Starefossen/snekkerbua/prosjekter/hanna/docs/generated/kappliste.md

<!-- GENERERT AV generate_loftbed.py / tools/gen_doc_tables.py.
     IKKE REDIGER FOR HÅND - kjør `mise run build`. -->

# Kappliste

Alle mål i mm. Alle kutt er 90° på to nær — se merknaden under tabellene. Posisjonen er delens plass i modellen: X langs veggen (0 = venstre vegg, 1990 = høyre vegg), Y i dybden (-48 = bakveggen), Z opp fra gulvet.

Lista står i to bolker, og skillet er en regel: **en del som kommer nærmere enn 5 mm fra en endevegg, eller som står på gulvet, får sluttmålet sitt av rommet — ikke av modellen.** Rommet er hverken i vinkel eller i vater. Resten kappes ferdig på bukken.

Mål rommet før du kapper romdelene: se [byggesteg](byggesteg.md#før-steg-0--mål-rommet).

## Kapp nå — verksteddeler

| Del | Dim. | Lengde | Ant. | X | Y | Z |
|---|---|---:|---:|---|---|---|
| Løs plate | 18 mm plate, 574 bred | **798** | 1 | 708..1282 | -48..750 | 297..315 |
| Benkespile | 23×98 | **800** | 10 | 98..1892 (fordelt) | -48..752 | 297..320 |
| Køyespile | 23×98 | **800** | 14 | 20..1970 (fordelt) | -48..752 | 1500..1523 |
| Rekkverksavstiver | 23×98 | **180** | 8 | 157,4..1832,6 (fordelt) | 752..775 | 1721..1901 |
| Benkespileledd | 36×48 | **547** | 2 | 98..1892 (fordelt) | 704..740 | 249..297 |
| Stigekloss | 36×48 | **36** | 8 | 835..1155 (fordelt) | 752..788 | 201..1194 (fordelt) |
| Endebjelke | 36×98 | **836** | 2 | 98..1892 (fordelt) | -48..788 | 1304..1402 |
| Fotbrettgavl (løs del) | 36×98 | **272** | 2 | 787..1203 (fordelt) | 216..488 | 0..98 |
| Benkevange, bak (gjennomgående) | 48×68 | **1794** | 1 | 98..1892 | -48..0 | 229..297 |
| Bordbærelekt, bak | 48×68 | **1794** | 1 | 98..1892 | -48..0 | 614..682 |
| Avstivningslekt under plate | 48×68 | **750** | 2 | 785..1205 (fordelt) | 0..750 | 229..297 |
| Benkevange, front (bit) | 48×68 | **547** | 2 | 98..1892 (fordelt) | 740..788 | 229..297 |
| Fotbrettbord | 48×68 | **416** | 4 | 787..1203 | 216..488 (fordelt) | 98..146 |
| Rungetrinn | 48×68 | **320** | 4 | 835..1155 | 720..788 | 249..1242 (fordelt) |
| Kilelekt under platens forkant (skråkappet) | 48×68 | **77** | 2 | 708..1282 (fordelt) | 702..750 | 229..297 |

**63 deler.** Rommet bestemmer ingen mål på disse. Kapp dem ferdig med én gang.

## Kapp når rommet er ferdig — romdeler

| Del | Dim. | Lengde | Ant. | Kapp på stedet | X | Y | Z |
|---|---|---:|---:|---|---|---|---|
| Endespile | 23×98 | **764** | 2 | nominell — bredden strekes opp | 0..1990 (fordelt) | -12..752 | 297..320 |
| Stigevange | 36×48 | **1871** | 2 | **+20** — trimmes i bunn | 787..1203 (fordelt) | 752..788 | 0..1871 |
| Endelist | 36×48 | **98** | 2 | **+10** i veggenden — finkappes | 0..1990 (fordelt) | -12..24 | 249..297 |
| Endelist, fremre | 36×48 | **98** | 2 | **+10** i veggenden — finkappes | 0..1990 (fordelt) | 716..752 | 249..297 |
| Hjørnestolpe, front | 36×98 | **2037** | 2 | **+20** — trimmes i bunn · siden mot veggen strekes opp ved bul | 0..1990 (fordelt) | 752..788 | 0..2037 |
| Hjørnestolpe, bak (veggside) | 36×98 | **1402** | 2 | **+20** — trimmes i bunn · siden mot veggen strekes opp ved bul | 0..1990 (fordelt) | -48..-12 | 0..1402 |
| Rekkverksbord, front | 36×98 | **832** | 4 | **+10** i veggenden — finkappes | 3..1987 (fordelt) | 716..752 | 1653..1969 (fordelt) |
| Stubbefot | 48×68 | **229** | 4 | **+20** — trimmes i bunn | 577..1413 (fordelt) | -48..788 (fordelt) | 0..229 |
| Sidevange, øvre | 48×98 | **1984** | 2 | **+10** i hver ende — finkappes | 3..1987 | -48..752 (fordelt) | 1402..1500 |

**22 deler.** Kapp dem med overmålet i kolonnen «Kapp på stedet», og finkapp på stedet:

* **Står på gulvet:** kapp 20 mm for lang. Gulvet legges først. Så trimmes foten til rammen står i vater. Strek opp med avstandskloss — meddrag.
* **Står på gulvet inntil endevegg — hjørnestolpene:** samme trimming i bunn, og i tillegg strekes siden. Stolpen står helt inntil veggen uten klaring, så en bul i veggen må tas i treet: hold stolpen i lodd på plass, strek opp veggsiden med avstandskloss og høvle av til den står i lodd inntil veggen. Ikke legg på noe i bredden — den nominelle dimensjonen står, det er bare bulen som går av.
* **Går fra vegg til vegg:** kapp 10 mm for lang i hver ende som møter vegg. Finkapp etter målt nisjebredde.
* **Bredden mot veggen:** kappes på nominell lengde. Det er BREDDEN som tilpasses, ikke lengden — ytterkanten strekes opp etter veggen så fugen blir jevn.

Kapp kanter som møter vegg eller gulv med lite bakfall. Da er det bare den synlige kanten som bestemmer fugen.

**85 deler i alt.**

«(fordelt)» betyr at delene i den raden står på flere posisjoner langs den aksen; kolonnen viser da hele området de dekker. Nøyaktige posisjoner står i [nøkkelmål](nokkelmal.md).

**Ett unntak fra «alle kutt er 90°»:** de to kilelektene under platens forkant. De sages i ett rett snitt fra full 68 mm ved roten — enden som støter mot styrelekta — ned til 27 mm ved tuppen på platens ytterkant, altså 28,0° på langs. Overkanten, den som limes mot plata, blir stående urørt i hele lengden. Håndsag eller båndsag; se steg 0 og J13b.

## Hjelpedeler — kappes, men bygges ikke inn

| Del | Dim. | Lengde | Ant. | Kapp | Brukes til |
|---|---|---:|---:|---|---|
| Vinkelkloss 25° (J8-B) — borjigg for skråskruen | 48×68 | **200** | 2 | 2 stk. skrus FLATE MOT FLATE til én kloss. ⌀18 bores VINKELRETT gjennom begge mens klossen ennå er firkantet — det er hele trikset. Først DERETTER kappes sålen av under hullet: kappsag med bladet vippet 25°, som gir en såle som står 65° på den borede flaten og dermed 25° på hullaksen. Kontrollmål: hullets munning i sålen er en ellipse på 42,6 × 18 mm — er den for kort, ble vippen satt på komplementvinkelen | klemmes mot flaten med TO tvinger, hullet over merket. ⌀18 forstnerbor og deretter forboret går NED I hullet, så boret ikke kan vandre. Dybdemerke: hold boret i jiggen til randen flukter med sålen ved hullaksen, merk av på skaftet og flytt merket 20 mm opp — det er setedybden. Brukes i J8-B |
| Vinkelkloss 30° (J10) — borjigg for skråskruen | 48×68 | **200** | 2 | 2 stk. skrus FLATE MOT FLATE til én kloss. ⌀18 bores VINKELRETT gjennom begge mens klossen ennå er firkantet — det er hele trikset. Først DERETTER kappes sålen av under hullet: kappsag med bladet vippet 30°, som gir en såle som står 60° på den borede flaten og dermed 30° på hullaksen. Kontrollmål: hullets munning i sålen er en ellipse på 36 × 18 mm — er den for kort, ble vippen satt på komplementvinkelen | klemmes mot flaten med TO tvinger, hullet over merket. ⌀18 forstnerbor og deretter forboret går NED I hullet, så boret ikke kan vandre. Dybdemerke: hold boret i jiggen til randen flukter med sålen ved hullaksen, merk av på skaftet og flytt merket 18 mm opp — det er setedybden. Brukes i J10 |

Disse er ikke med i de 85 delene over — de er ikke deler i senga, de er verktøy du sager i steg 0. Virket til dem er likevel med i [innkjøpslista](innkjopsliste.md): de står i kappeplanen for sin egen dimensjon, som alt annet du må sage.

Fordelt på dimensjon: **23×98** 34 stk. · **48×68** 20 stk. · **36×48** 16 stk. · **36×98** 12 stk. · **48×98** 2 stk. · **18 mm plate, 574 bred** 1 stk.

Sagstopp for hovedbordet 36×98: **2 stk. à 2037** · **2 stk. à 1402** · **2 stk. à 836** · **4 stk. à 832** · **2 stk. à 272** — 5 innstillinger på sagen, ikke én per del.
