Starefossen/snekkerbua/prosjekter/hanna/docs/generated/nokkelmal.md

<!-- GENERERT AV generate_loftbed.py / tools/gen_doc_tables.py.
     IKKE REDIGER FOR HÅND - kjør `mise run build`. -->

# Nøkkelmål

Alle mål i mm. X går langs rommet mellom de to veggene, Y i dybden med bakveggen på -48, Z opp fra gulvet.

## Ytre mål

| | Mål |
|---|---:|
| Bredde, vegg til vegg | 1990 |
| Dybde over alt | 836 |
| Høyde foran (stolpetopp) | 2037 |
| Høyde ved veggen (bakre stolpe) | 1402 |
| **Takhøyde i rommet senga er regnet for** | **2450** |
| Klaring over høyeste del | 413 |
| **Fri høyde under senga (gulv til spilenes underside)** | **1500** |
| Fri høyde over øvre madrass | 807 |
| Gjennomgående deler kappes til | 1984 (X 3..1987) |
| Klaring til hver vegg for disse | 3 |

En 1990 mm lang del lar seg ikke svinge inn i en 1990 mm åpning. Derfor er hver gjennomgående del 1984 mm.

## Høyder (Z)

| Z | Hva |
|---:|---|
| **0** | gulv |
| **229** | benkevangens underkant / stubbefotens topp |
| **297** | benkevangens overkant = trinn 1 = platens underside i sengestilling |
| **315** | platens overside i sengestilling |
| **320** | benkeoverflate (sittehøyde uten pute) |
| **420** | **puteoverflate — nedre soveflate og sittehøyde med pute** (V13) |
| **614** | bordbærelektas underkant |
| **634** | støttetrinnets underkant |
| **682** | trinn 2 = bordbærelektas og STØTTETRINNETS overkant = platens underside i bordstilling (X16: et trinn igjen; X9 hadde to bordklosser her) |
| **700** | **bordplate — pulthøyde** (X9) |
| **752** | ryggputens topp i sofastilling (V13) |
| **962** | trinn 3 |
| **1242** | trinn 4 |
| **1304** | endebjelkens underkant |
| **1402** | **bakre stolpetopp** = endebjelkens overkant = sidevangens underkant (fri høyde under sengen) |
| **1500** | sidevangens overkant |
| **1523** | spilebunn / madrassens underside |
| **1643** | madrassens overside (ved 120 mm madrass; lovlig band 105–130) |
| **1653** | rekkverk, nedre bånd underkant |
| **1751** | rekkverk, nedre bånd overkant |
| **1871** | rekkverk, øvre bånd underkant |
| **1969** | rekkverk, øvre bånd overkant |
| **2037** | fremre stolpetopp |

Stigningen fra gulv til spilebunn: 297 + 385 + 280 + 280 + 281 mm. Første stigning er benkevangens høyde — det er en avsats du trår opp på, ikke et klatretrinn. De 4 klatretrinnene er 280–385 mm.

## Dybdeplan (Y)

| Y | Hva |
|---:|---|
| **-48** | BAKVEGGEN — monteringsflaten. Bakre stolper, endebjelkeender og bakre stubbeføtter ligger i dette planet. Ingenting får stikke bak det.; bakre sidevange, benkevange, bordbærelekt og spilebunn — bakkant; bakre stolpes forside |
| **0** | bakre sidevanges, benkevanges og bordbærelektas forside; avstivningslektenes bakkant |
| **704** | fremre sidevange og benkevange — bakkant |
| **716** | rekkverksbordenes bakkant |
| **720** | trinnenes bakkant (hylla platen hviler på) |
| **750** | platens forkant; avstivningslektenes og kilelektenes forkant |
| **752** | fremre sidevanges forside = fremre stolpers og stigevangers bakside = spilebunnens forkant; rekkverksbordenes forkant |
| **788** | fremre stolpers og stigevangers forside = trinnenes forkant; sengens forkant — det ytterste planet |

Fri bredde mellom de to sidevangene: **704**. Spilebunnen fra vange til vange: **800** — nøyaktig madrassbredden.

## Stige, trinn og rekkverk (X)

| | X |
|---|---|
| Stigens senterlinje | 995 |
| Stigevanger | 787..835 og 1155..1203 |
| Fri åpning mellom stigevangene | **320** |
| Trinn (4 stk.) | 835..1155, 320 mm lange |
| Stigeklosser | 835..871 og 1119..1155 |
| Rekkverksbord | 3..835 og 1155..1987 |
| Klatreåpning i begge rekkverksbånd | **320** |
| Benkene | 0..645 og 1345..1990 |
| Åpent gulv mellom benkene | 645..1345 (700 mm) |
| Gangpassasje ved siden av stigen | 142 mm på hver side |
| Stubbeføtter | 577..645 og 1345..1413 |
| Løs plate | 708..1282 (574 mm bred) |
| Avstivningslekter (styrer platen) | 785..833 og 1157..1205 |
| Kilelekter under forkanten | 708..785 og 1205..1282 |
| Klaring lekt → trinnende | 2 mm hver vei (trinnendene står på X 835 og 1155 i begge stillinger) |

### Platebredden er kvantisert — lovlige vinduer

Åpningen mellom benkene er fast, **700 mm**, så sideklaringen er `(700 − bredde) / 2` på hver side. EN 747 gjør bare tre klaringsbånd lovlige — under 5 mm kommer ikke fingeren inn, 12–25 mm går den fritt gjennom, 60–75 mm går hele lemmet fritt og åpningen er fortsatt under EN 747s egen 75 mm-grense — og mellom båndene kiler fingeren seg. Bredden er derfor ikke en skrue man vrir på: den lander i ett av tre vinduer, eller så er den ulovlig.

| Klaringsbånd | Lovlig platebredde | |
|---|---|---|
| 60–75 mm | 550–580 mm | **valgt — 574 mm, 63 mm klaring** |
| 12–25 mm | 650–676 mm | tidligere vindu (652 mm) |
| 0–5 mm | 690–700 mm | upraktisk — spiser opp de 2 mm innsettingsklaring |
| — | **581–649 mm** | **forbudt** — klaringer 25,5–59,5 mm, midt i klembåndet |
| — | **677–689 mm** | **forbudt** — klaringer 5,5–11,5 mm, midt i klembåndet |

Bredden deltar **ikke** i begrensningene på stillingsbyttet — det er høyden og dybden på plateenheten som møter overføringssjakten (294 mm fri høyde mot en 86 mm høy enhet). Å smalne platen gir mer slingring ved innsettingen og mindre bordflate, ingenting annet. Modellen asserter vinduene: en «bare litt smalere»-endring stopper byggeporten med akkurat denne tabellen.

**Køyespiler:** 14 stk., første spile starter på X 20, deling 142,46 mm, siste spile slutter på X 1970. Åpning mellom spilene 44,46 mm.

**Benkespiler:** 5 per benk, deling 112,25 mm, felt X 98..645 (speilvendt på den andre benken).

**Endespiler (V13):** 1 per benk, 764 mm lang, X 0..98 og 1892..1990, Y -12..752. Den er kortere fordi den starter på den bakre hjørnestolpens forside, og den lukker feltet helt ut til veggen — spalten inn til første benkespile er 0 mm. Uten den stopper soveflaten nede 98 mm fra veggen i hver ende. Endelisten under den er 36×48 × 98 mm, skrudd på stolpens forside (J17).

## Skruerader i rammeleddene

Ingen bolt går inn i en stolpe. Stolpen er 36 mm tykk, og på den tykkelsen har en M8 ikke nok kantavstand; en 6 mm treskrue har akkurat nok. To skruer i et ledd står alltid symmetrisk om delens midtlinje. Skruetyper og antall står i [beslaglista](beslagliste.md).

| Ledd | Skruer | Z | Kantavstand | Avstand mellom | I planet |
|---|---:|---|---|---:|---|
| J1 — endebjelke 36×98 | 2 per ledd | **1323** og **1367** | 19 / 35 | 44 | Y -30 og 770 (midt i stolpedybden) |
| J2 — sidevange 48×98 | 2 per ledd | **1429** og **1473** | 27 / 27 | 44 | X 50,5 fra hver vegg |
| J8 — benkevange 48×68 | 2 per ledd | **253** og **277** | 24 / 20 | 24 | X 119,87 fra hver vegg |

Minstekrav for en forboret 6 mm treskrue: kantavstand 18 mm (3d), avstand mellom to skruer langs fiberretningen 30 mm (5d). Alle radene over holder kravet.

Endeavstanden fra vangens ende inn til J2- og J8-skruen er 47,5 mm, godt over minstekravet 18 mm — den brede stolpen ga denne avstanden gratis.

**Ingen forsenkte boltehoder.** Ingen del av rammen festes lenger fra en flate som ender mot vegg, så det finnes ikke et eneste hode som må senkes ned under en monteringsflate. Skruehoder forsenkes som vanlig der de er i veien for hånda.

## Madrass og puter

| | Mål |
|---|---|
| Madrass, overkøye | **standard 80 × 200 cm.** Sengen er dimensjonert rundt den; liggeflaten er 1990 × 800 mm, så madrassen presses de siste 10 mm inn mellom veggene og fyller bredden nøyaktig |
| **Madrasstykkelse** | **105–130 mm — kjøp 120 mm.** Åpningen fra madrassens overside opp til nedre rekkverksbånd skal enten være LUKKET — under 25 mm, der ingenting kommer inn — eller ligge i EN 747-båndet 60–75 mm, der hele lemmet går fritt igjennom. Mellom de to, 25–60 mm, er klemvinduet. Det bygde rekkverket står 130 mm over spilene, så vinduet er den LUKKEDE grenen: tynnere enn 105 og åpningen vokser opp i klemvinduet; **tykkere enn 130 og madrassen står inne i selve rekkverksbordet — bordet dekker ikke lenger kanten, det ligger begravet i den**. Hyllevarene utenfor vinduet — 100, 140, 150, 160 mm — er altså ULOVLIGE her, og det er ikke en detalj: det er den ene tingen ved denne sengen du må huske i butikken. Modellen tegner 120 mm, som gir 10 mm — bordet ligger like over madrassen og dekker forkanten |
| **Maks madrasstykkelse merkes på sengen** | 130 mm. EN 747 krever at maksmålet står permanent på sengen. Merk linja 1653 mm over gulvet — 130 mm over spilene — på innsiden av en fremre stolpe (steg 11) |
| Madrassens sideveis vandring | ingen — madrassen fyller hele bredden mellom veggen og de fremre stolpene |
| **Soveflate, underetasjen** | **1990 × 800 mm** — samme lengde som overkøyen. De to bakre hjørnestolpene står i flaten og tar et 98 × 36 mm hjørne i hver ende; ellers er den hel |
| **Puter, tykkelse** | **100 mm, alle fire.** Lik tykkelse er hele poenget: fire like tykke puter er én seng. Sittehøyden blir 320 + 100 = **420 mm** |
| Puter, dybde | 800 mm — hele flatens dybde, vegg til fremre stolpeplan |
| **Benkepute (2 stk.)** | **663 × 800 × 100 mm** — 1/3 av lengden. Skjær et 98 × 36 mm hakk i veggkanten, der stolpen står |
| **Ryggpute (2 stk.)** | **332 × 800 × 100 mm** — 1/6 av lengden. Rene rektangler |
| Regnestykket | 663 + 332 + 332 + 663 = **1990 mm**. 1990 deler seg ikke på 6, så tredelen er rundet ned og sjettedelen opp — summen er eksakt, og det er summen som må stemme |
| Alle fire av én skumplate | 80 × 200 cm dekker dem: 800 mm er nøyaktig dybden og 2000 mm er 10 mm mer enn lengden. Fire tverrkapp |
| Midtsonen ligger | 5 mm lavere enn benkene (415 mot 420 mm). Putene er like tykke likevel — skummet tar de 5 millimeterne, og ingen puteskjøt ligger på en sonegrense |
| Hodehøyde over nedre soveflate | 1080 mm til køyespilene (982 mm under sidevangene) — men det er høyden i det ÅPNE feltet. Målt på kroppene over hele soveflatens fotavtrykk er laveste faste del «Table Ledger Back» på 194 mm, og over putestripa langs veggen er det «Table Ledger Back» på 194 mm |
| Ryggpute i sofastilling | står på høykant ytterst på hver benk: 100 mm tykk, 800 mm dyp, 332 mm høy, topp 752 mm. Ryggen mot bordbærelekta |

## Kasserommet under benkene

Under hver benk står det et rom som ikke er tegnet inn — det er bare det stubbeføttene lar bli igjen — og her er målene på det, målt på delene. **Kasser inntil 229 × 479 × 800 mm (H × B × D) går inn, én på hver side.** De skyves rett inn forfra, under benkevangen.

| | Mål |
|---|---:|
| **Fri høyde** | **229 mm** — gulv til benkevangens underkant |
| **Fri bredde** | **479 mm** — fra bakre hjørnestolpes innerside til stubbefotens ytterside (X 98–577 og 1413–1892) |
| **Fri dybde** | **800 mm** — veggen til fremre benkevanges forside, altså hele benkens dybde. Benkevangen henger over kassa, ikke foran den |
| Antall rom | 2 — ett under hver benk. Mellom dem er gulvet åpent foran stigen (X 645–1345), og der skal det ikke stå noe |
| Hva som stjeler resten | de fire stubbeføttene (68 mm hver i X, innerst på hver benk) og de to bakre hjørnestolpene (98 mm hver, ytterst) |
| Høyden er et minstemål | gulvet er skjevt og rammen bygges i vater fra høyderisset over gulvets HØYESTE punkt, så 229 mm er høyden akkurat der — ellers er det mer. Mål på stedet før du kapper en kasse i mannshøyde med tallet |

## Referansekroppen — hva sengen er til for

Modellen har fire *referansekropper*: et barn på **1200 mm** (EN 747 åpner overkøya fra 6 år), bygget som én solid av 14 kuler, sylindre og bokser med segmentene som brøkdeler av ståhøyden etter **AnthroKids** (de digitaliserte Snyder-studiene 1975/1977, math.nist.gov/~SRessler/anthrokids/, fri bruk). To ligger i sengestilling, to sitter i bordstilling. En kropp er ikke en del: den kappes ikke, bærer ingenting, står i ingen liste og er tatt ut av alle kontaktsjekker — men den er i parts.tsv og i eksportene, og målene under er målt på den.

| | Mål |
|---|---:|
| **Fri høyde over hodet, sittende** | **426 mm** — kronen står i Z 1074 og «Bed Slat_8» er det første over. Man sitter helt rett opp i sofaen |
| Sittehøyde | 654 mm (0,545 × H) over seteflaten på 420 mm |
| **Bordplaten over setet** | **280 mm**, med 262 mm under seg — et sittende kne står 135 mm over setet, så KNÆRNE går inn under platen med 127 mm luft. Det er hele X9-runden: en PULT, ikke et sofabord. Fram til v15 lå platen 140 mm over setet med 122 under seg, og 122 slipper et lår inn men ikke et kne — derfor satt figurene i skredderstilling helt til nå |
| Nærmeste kropp til platen, sittende | 71 mm |
| Underarmen over platen | 6 mm — barnet legger armene oppå og har albuene i været: 92 mm av platehøyden ligger over albuen til et barn på 1200 mm. Det er en pulthøyde regnet for en stol, brukt fra en sofa — SMÅSTAD-pulten på 730 over den 430 mm stolen som selges til den gjør det samme (300 mm) |
| **Sålene på fotbrettet** | **146 mm** over gulvet — de HENGER ikke: leggen står i lodd, foten ligger flatt og kneet på 97°. Til og med X9 hang de 134 mm i lufta |
| Fotbrettets høyde | 146 mm — utledet, ikke valgt: setet bærer låret bare så lenge sålen står mellom 135 og 154 mm, og av de 9 kurvene sengens egne fem dimensjoner lager treffer én båndet (98 på høykant + 48 flatt) |
| Fotbrettets plass | X 787..1203 × Y 216..488 × Z 0..146 — bukta mellom de to gangpassasjene, løs, under platen i begge stillinger (151 mm / 536 mm luft) |
| Låret på puta | barnet står 12.7 mm ned i skummet — samme dybde som rumpa selv (12.7 mm), og puta bærer låret helt ut til sin egen kant på X 663 |
| **Fri høyde over ansiktet, nede** | **902 mm** til køyespilene |
| Over den som ligger i køya | ingenting — køya er åpen oppover. Rekkverket står 83 mm over kroppens høyeste punkt og 148 mm over ansiktet |
| Madrass igjen bak føttene | 588 mm av 1990 — plassen å vokse i |

## Sikkerhetsmål (EN 747)

| | Mål | Krav |
|---|---:|---:|
| Madrassoverside → nedre rekkverksbånd | 10 | ≤ 25 (lukket) eller 60–75 |
| Mellom de to rekkverksbåndene — 120 mm delt av 4 avstivere per felt, smaleste vei | 59,4 | ≤ 75 |
| Øvre rekkverksbånd → fremre stolpetopp | 68 | ≤ 75 |
| Klatreåpningens bredde | 320 | 300–400 |
| Rekkverkets høyde over madrassen | 326 | ≥ 160 |
| Åpning mellom madrass og vegg (verste stilling) | 0 | ≤ 75 |
| Fri klatreåpning i stigen | 320 | ≥ 300 |
| Største klatretrinn i stigen selv | 385 | ≤ 281 |
| — største steg på veien barna faktisk går (297 → 420 → 682, over benkekanten) | 262 | ≤ 281 |
| Hodehøyde over nedre soveflate | 1080 | ≥ 900 (én sittehøyde) |
| — laveste faste del over soveflaten (målt) | 194 (Table Ledger Back) | ingen grense — det er stigen |
| — over putestripa ved veggen (målt) | 194 (Table Ledger Back) | ingen grense — lekta er permanent |
| Hodehøyde over øvre madrass | 807 | ≥ 750 (køya er sovesone) |
