Starefossen/snekkerbua/prosjekter/hanna/docs/generated/beslagliste.md

<!-- GENERERT AV generate_loftbed.py / tools/gen_doc_tables.py.
     IKKE REDIGER FOR HÅND - kjør `mise run build`. -->

# Beslag og festemidler

Alt er elforsinket eller varmforsinket. Handelsnavn som i norsk byggevarehandel.

## Handleliste

| Post | Behov | Kjøp |
|---|---:|---|
| Treskrue 5×60 forsenket Torx | 92 | 1 pk. à 100 stk. |
| Treskrue 5×40 forsenket Torx | 48 | 1 pk. à 50 stk. |
| Treskrue 6×80 forsenket Torx | 38 | 1 pk. à 50 stk. |
| Treskrue 6×120 forsenket Torx | 16 | 1 pk. à 20 stk. |
| Veggfeste etter veggtype (treskrue 8×100 i stender, eller plugg + skrue i mur) | 9 | 9 stk. |
| Filtknott / møbeltapp ⌀40 | 8 | 1 pk. |

**Behov** er antallet sengen bruker; **Kjøp** er den minste pakken som finnes i butikk og dekker behovet. Treskruer selges i pakker à 8 / 20 / 25 / 50 / 100 / 200 stk. Står det samme tall i begge kolonnene, har du ingen reserve — ta en pakke opp. En skrue du mangler koster en kveld.

I tillegg trengs **D3 trelim**, én liten flaske. Den er ikke en post i tabellen fordi den ikke telles i stykk, men den er ikke valgfri: J13a og J13b er limte fuger, og skruene der er tvinger som blir sittende.

## Hvor det går — ledd for ledd

| Ledd | Hva | Antall ledd | Per ledd | Forboring | Drives fra |
|---|---|---:|---|---|---|
| **J1** | Endebjelke → hjørnestolpe | 4 | 2× Treskrue 6×80 forsenket Torx | ⌀6 gjennom bjelken, ⌀4 i stolpen | Fra bjelkens innside (mot sengas midte), inn mot stolpen — helt inne i sengen, tilgjengelig hele veien. Disse to skruene er HELE festet: det står ingen kloss under bjelkeenden |
| **J2** | Fremre sidevange → fremre hjørnestolpe | 2 | 2× Treskrue 6×80 forsenket Torx | ⌀6 gjennom vangen, ⌀4 i stolpen | Fra vangens innside — inne fra sengen — gjennom vangen og inn i stolpen. Stolpens forside er urørt |
| **J2-B** | Bakre sidevange → bakre hjørnestolpe (vangen hviler på stolpetoppen) | 2 | 2× Treskrue 6×120 forsenket Torx | ⌀6 gjennom vangen, ⌀4 i stolpens endeved; forsenk hodet godt under vangens overkant så køyespilene ligger flatt | Rett ned gjennom vangen i stolpetoppen, mens bakrammen ligger flatt på gulvet. Ingenting på veggsiden, og ingen kloss: vangen står 12 mm proud av den tynnere stolpen, så et rett beslag ville uansett ikke ligget an mot begge |
| **J3** | Stigevange → fremre sidevange | 2 | 3× Treskrue 6×80 forsenket Torx | ⌀6 gjennom sidevangen, ⌀4 i stigevangen | Fra sidevangens innside — inne fra sengen — gjennom vangen og inn i stigevangen. Stigevangens forside er urørt |
| **J4** | Rungetrinn → stigevange (per trinnende) | 8 | 1× Treskrue 6×120 forsenket Torx | ⌀6 gjennom stigevangen inn i trinnenden, ⌀4 i trinnet | 6×120 fra utsiden av stigevangen, inn i trinnets endeved. Ingenting gjennom trinnets overside — trinnet ligger på stigeklossen og klossen har sin egen skrue (J5) |
| **J5** | Stigekloss → stigevange | 8 | 1× Treskrue 5×60 forsenket Torx | ⌀3,5 gjennom klossen, ⌀3 i vangen | Fra stigeåpningen, inn i vangens innside |
| **J6** | Køyespile → sidevange (per spileende) | 28 | 1× Treskrue 5×60 forsenket Torx | ⌀3,5 gjennom spilen, forsenk hodet under flaten | Ovenfra, ned i vangen |
| **J7** | Rekkverksbord → hjørnestolpe / stigevange (per omlegg) | 6 | 2× Treskrue 5×60 forsenket Torx | ⌀3,5 gjennom bordet, ⌀3 i stolpen | Fra sengesiden, inn i stolpens/stigevangens innside |
| **J21** | Rekkverksavstiver → rekkverksbord (per omlegg, X18) | 16 | 2× Treskrue 5×40 forsenket Torx | ⌀3,5 gjennom avstiveren, ⌀3 i bordet, forsenk hodet | Fra rommet, rett inn i bordets utside. Avstiveren ligger i sporet mellom stolpeplanet og bordet, så den står 13 mm innenfor forflaten og ingenting av den kommer inn i sengeflaten |
| **J8** | Fremre benkevange → fremre hjørnestolpe (endeskjøt) | 2 | 2× Treskrue 6×80 forsenket Torx | Først sete: ⌀18 forstner 20 mm ned LANGS skruens akse, med den samme vinkelklossen som J8-B bruker. Så ⌀6 skrått videre gjennom vangen og ⌀4 i stolpen — forbor hele veien, dette er en skråskrue nær en ende | Skrått fra vangens innside — inne fra benkerommet — inn i stolpen, ut av et flatbunnet sete så hodet ligger helt under treet. Vangen står buttet mellom stolpen og stigevangen, og disse to skruene er HELE festet i denne enden |
| **J8-B** | Bakre benkevange → bakre hjørnestolpe (endeskjøt) | 2 | 2× Treskrue 6×80 forsenket Torx | Først sete: ⌀18 forstner 20 mm ned LANGS skruens akse, med vinkelklossen som styring. Så ⌀6 skrått videre gjennom vangen og ⌀4 i stolpen — forbor hele veien, dette er en skråskrue nær en ende | Skrått fra vangens forside inn i stolpen, ut av et flatbunnet sete så hodet ligger helt under treet. Vangen ligger fast mellom de to stolpene, og disse to skruene er HELE festet i enden — det står ingen kloss under den |
| **J10** | Benkevange → stubbefot | 4 | 1× Treskrue 6×120 forsenket Torx + 1× Treskrue 5×60 forsenket Torx | ⌀3 i foten og i vangen. Skråskruen får først sete: ⌀18 forstner 18 mm ned langs skruens akse, med vinkelklossen som styring, så ⌀3,5 videre | Én skrue rett NEDENFRA OG OPP gjennom vangen i foten (6×120, hodet forsenket i vangens overkant under spilene) og én skråskrue FRA SIDEN, ut av et flatbunnet sete i fotens innerside så hodet ligger helt under treet. Ikke noe beslag — X18: byggherrens «skruer ovenfra og fra siden» |
| **J11** | Benkespile → bakre benkevange (bakre spileende) | 10 | 1× Treskrue 5×60 forsenket Torx | ⌀3,5 gjennom spilen, forsenk hodet under flaten | Ovenfra, ned i benkevangen |
| **J11-F** | Benkespile → benkespileledd (fremre spileende, X18) | 10 | 1× Treskrue 5×60 forsenket Torx | ⌀3,5 gjennom spilen, forsenk hodet under flaten | Ovenfra, ned i leddet på den fremre benkevangens innside — spileenden ligger på ledd og vange i ett plan, og skruen står i leddet |
| **J19** | Benkespileledd → fremre benkevange (X18) | 8 | 1× Treskrue 5×60 forsenket Torx | ⌀3,5 gjennom leddet, ⌀3 i vangen | Vannrett fra benkerommet, inn i vangens innside. Leddets overkant legges i flukt med vangens overkant — det er den ene linjen som må stemme |
| **J11-E** | Endespile → fremre endelist (fremre spileende) | 2 | 1× Treskrue 5×60 forsenket Torx | ⌀3,5 gjennom spilen, forsenk hodet under flaten | Ovenfra, ned i benkevangen |
| **J20** | Fremre endelist → fremre hjørnestolpe (mot stolpens bakside, X18) | 2 | 2× Treskrue 5×60 forsenket Torx | ⌀3,5 gjennom listen, ⌀3 i stolpen | Rett inn i stolpens bakside, fra benkerommet — listen ligger flatt på stolpen og de to skruene er hele festet |
| **J16** | Endespile → endelist (bakre spileende) | 2 | 1× Treskrue 5×60 forsenket Torx | ⌀3,5 gjennom spilen, forsenk hodet under flaten | Ovenfra, ned i endelisten |
| **J17** | Endelist → bakre hjørnestolpe (mot stolpens forside) | 2 | 2× Treskrue 5×60 forsenket Torx | ⌀3,5 gjennom listen, ⌀3 i stolpen | Rett inn i stolpens forside, fra benkerommet — listen ligger flatt på stolpen og de to skruene er hele festet |
| **J12** | Bordbærelekt → bakre hjørnestolpe (endeskjøt) | 2 | 2× Treskrue 6×80 forsenket Torx | ⌀3 i stolpen og i lekta — forboring er et krav: begge skruene står nær en ende, og lekta (48×68) tas i endeveden | Skrått fra lektas forside inn i stolpen, ut av et flatbunnet sete så hodet ligger helt under treet. Ikke noe beslag — X18: samme ledd som J8-B, en etasje opp |
| **J12-V** | Veggfeste — gjennom bordbærelekta inn i stenderne | 1 | 3× Veggfeste etter veggtype (treskrue 8×100 i stender, eller plugg + skrue i mur) | ⌀8 gjennom lekta, forsenk for hodet; veggen etter festetype. Bores på stedet — stenderne finnes bare i rommet | Rett gjennom lekta inn i veggen, fra benkerommet. Lekta ligger flatt mot veggen i hele sin lengde, så festet trenger verken kloss eller brakett; hodet forsenkes i lektas forside, som ryggputa lener seg mot |
| **J13a** | Avstivningslekt → løs plate (limt, skrudd nedenfra) | 2 | 6× Treskrue 5×40 forsenket Torx | ⌀12 kontrabor 41 mm opp i lektas underside, ⌀3,5 videre gjennom resten av lekta. Ingenting gjennom platens overside | Nedenfra, opp gjennom lekta og 13 mm inn i den 18 mm platen. Limes med D3 trelim på hele lektas overkant først — skruene er tvinger som blir sittende |
| **J13b** | Fremre kilelekt (vinge) → løs plate (limt, skrudd nedenfra) | 2 | 2× Treskrue 5×40 forsenket Torx | ⌀12 kontrabor opp i vingens underside TIL DET STÅR 27 mm IGJEN opp til plata — vingen er skråkappet, så det blir dypest ved roten og null ved tuppen. ⌀3,5 videre gjennom de siste 27 mm. Ingenting gjennom platens overside | Nedenfra, som J13a. Vingen ligger med forkanten i flukt med platens forkant, full høyde mot avstivningslekta og skråkappet ut mot platekanten |
| **J18** | Fotbrettbord → gavl | 8 | 1× Treskrue 6×80 forsenket Torx | ⌀6 gjennom bordet, ⌀4 i gavlens overkant, forsenk hodet under flaten — det er en flate føtter står på | Ovenfra, rett ned i gavlen |
| **J14** | Veggfeste — gjennom den bakre sidevangen inn i stenderne | 1 | 6× Veggfeste etter veggtype (treskrue 8×100 i stender, eller plugg + skrue i mur) | ⌀8 gjennom vangen, forsenk for hodet; veggen etter festetype | Rett gjennom vangen inn i veggen. Vangen ligger flatt mot veggen i hele sin lengde, så festet trenger ingen kloss og ingen brakett |
| **J15** | Filtknott under stolpe og stubbefot | 8 | 1× Filtknott / møbeltapp ⌀40 | — | Slås i endeveden før reisning |

Forklaringen til hvert ledd står i [ASSEMBLY.md](../ASSEMBLY.md#4-j--leddene).

## Lås i sengestilling — ingen, og det er et valg

**Det står ingen lås i denne lista, og det er ikke en glipp.** Platen løftes rett opp i begge stillinger, og etter denne runden er det ingen ståldel igjen i platemekanismen i det hele tatt — verken beslag eller lås.

Begrunnelsen står i sin helhet i [ASSEMBLY, vedlegg B, avvik 4](../ASSEMBLY.md#vedlegg-b--aksepterte-avvik). Kort: madrassen ligger *oppå* platen og må fjernes før platen kan løftes, dette er underetasjen med ~42 cm fallhøyde, og plateenheten veier 6,3 kg.

Trevirket for en ettermontert lås står likevel der det sto: **kilelektas endeved mot enden av den fremre benkevangen**, tvers over de 63 mm i sideklaringen, i samme høydebånd i sengestilling og 385 mm fra hverandre i bordstilling. Geometrien er målt og asserted i modellen, så en lås kan ettermonteres senere uten at noe tre må endres.
