Starefossen/snekkerbua/prosjekter/hanna/docs/img/beslag/vinkelbeslag-40x40x20.png

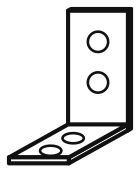
prosjekter/hanna/docs/img/beslag/vinkelbeslag-40x40x20.png
