Starefossen/snekkerbua/prosjekter/hanna/docs/img/beslag/vinkelbeslag-90x90x40.png

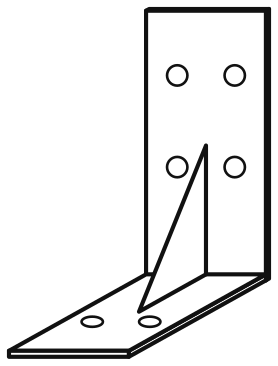
prosjekter/hanna/docs/img/beslag/vinkelbeslag-90x90x40.png
