Starefossen/snekkerbua/prosjekter/hanna/docs/img/bruk-bordstilling.png

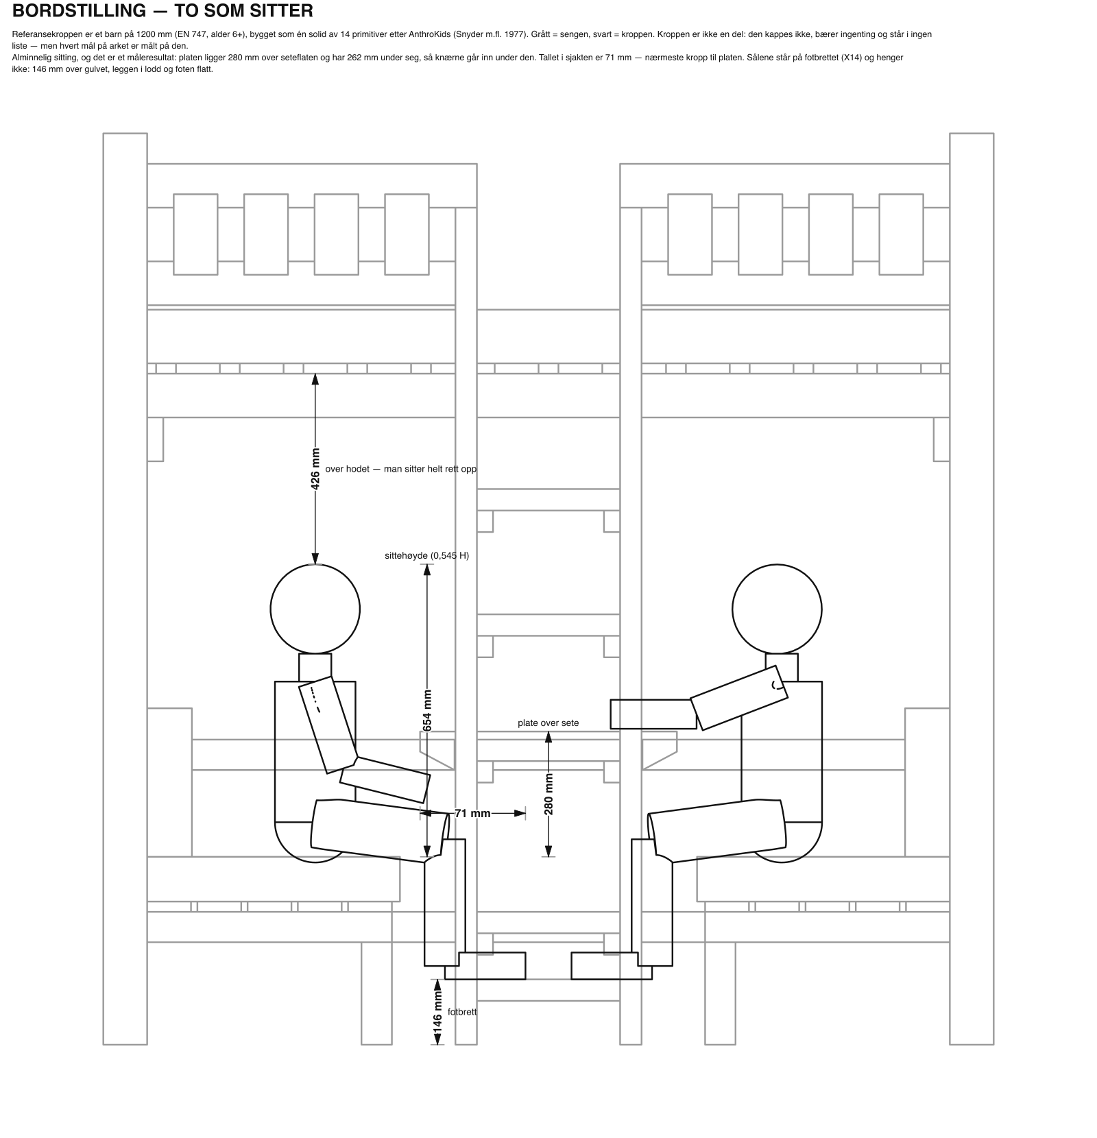
prosjekter/hanna/docs/img/bruk-bordstilling.png
