Starefossen/snekkerbua/prosjekter/hanna/docs/img/ikon/blyant-foerst.png

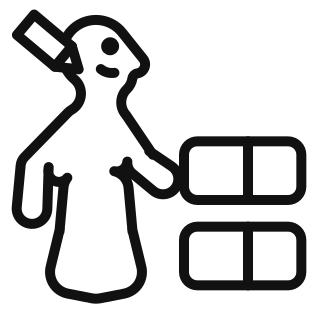
prosjekter/hanna/docs/img/ikon/blyant-foerst.png
