Starefossen/snekkerbua/prosjekter/hanna/docs/img/ikon/dra-nei.png

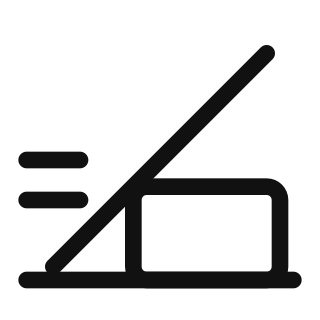
prosjekter/hanna/docs/img/ikon/dra-nei.png
