Starefossen/snekkerbua/prosjekter/hanna/docs/img/ikon/en-person-nei.png

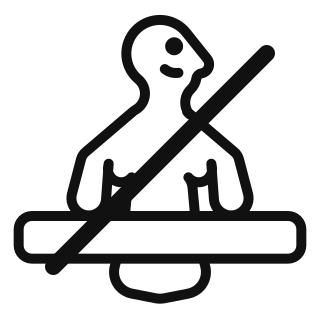
prosjekter/hanna/docs/img/ikon/en-person-nei.png
