Starefossen/snekkerbua/prosjekter/hanna/docs/img/ikon/forbor.png

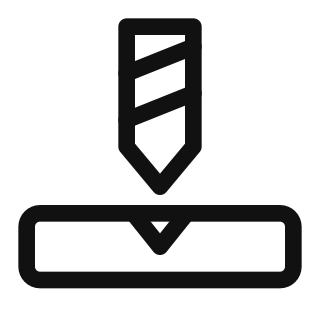
prosjekter/hanna/docs/img/ikon/forbor.png
