Starefossen/snekkerbua/prosjekter/hanna/docs/img/ikon/fritt-staaende-nei.png

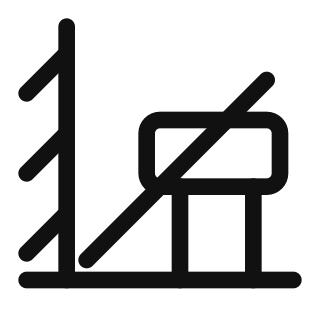
prosjekter/hanna/docs/img/ikon/fritt-staaende-nei.png
