Starefossen/snekkerbua/prosjekter/hanna/docs/img/ikon/hake.png

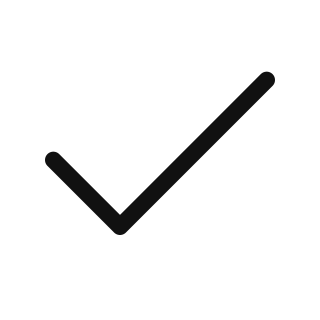
prosjekter/hanna/docs/img/ikon/hake.png
