Starefossen/snekkerbua/prosjekter/hanna/docs/img/ikon/info.png

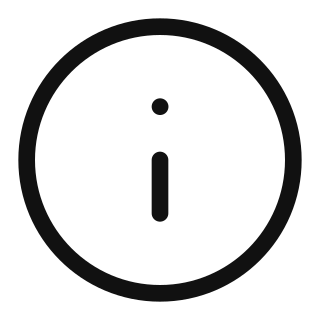
prosjekter/hanna/docs/img/ikon/info.png
