Starefossen/snekkerbua/prosjekter/hanna/docs/img/ikon/kryss.png

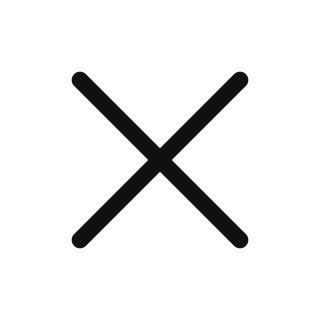
prosjekter/hanna/docs/img/ikon/kryss.png
