Starefossen/snekkerbua/prosjekter/hanna/docs/img/ikon/merke-a.png

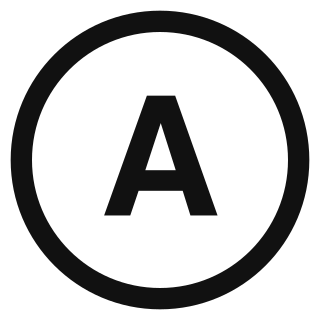
prosjekter/hanna/docs/img/ikon/merke-a.png
