Starefossen/snekkerbua/prosjekter/hanna/docs/img/ikon/merke-b.png

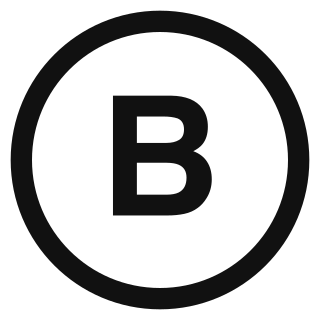
prosjekter/hanna/docs/img/ikon/merke-b.png
