Starefossen/snekkerbua/prosjekter/hanna/docs/img/ikon/punktmaal-nei.png

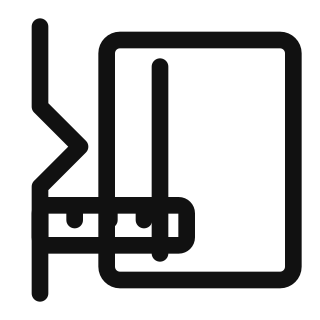
prosjekter/hanna/docs/img/ikon/punktmaal-nei.png
