Starefossen/snekkerbua/prosjekter/hanna/docs/img/ikon/skrutrekker-foerst-nei.png

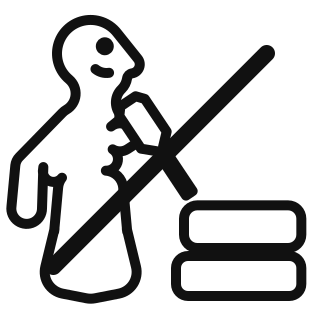
prosjekter/hanna/docs/img/ikon/skrutrekker-foerst-nei.png
