Starefossen/snekkerbua/prosjekter/hanna/docs/img/ikon/sorter.png

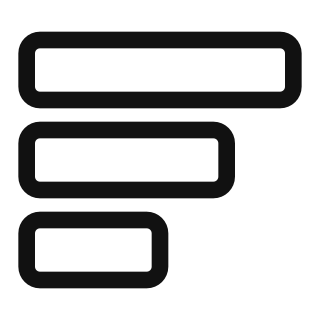
prosjekter/hanna/docs/img/ikon/sorter.png
