Starefossen/snekkerbua/prosjekter/hanna/docs/img/ikon/to-personer.png

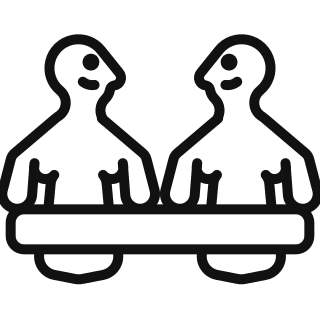
prosjekter/hanna/docs/img/ikon/to-personer.png
