Starefossen/snekkerbua/prosjekter/hanna/docs/img/ikon/underlag.png

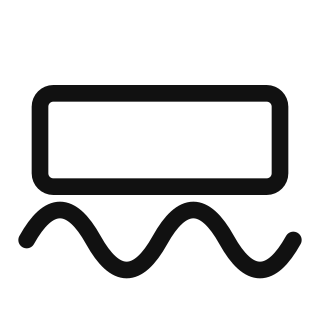
prosjekter/hanna/docs/img/ikon/underlag.png
