Starefossen/snekkerbua/prosjekter/hanna/docs/img/ikon/verktoy.png

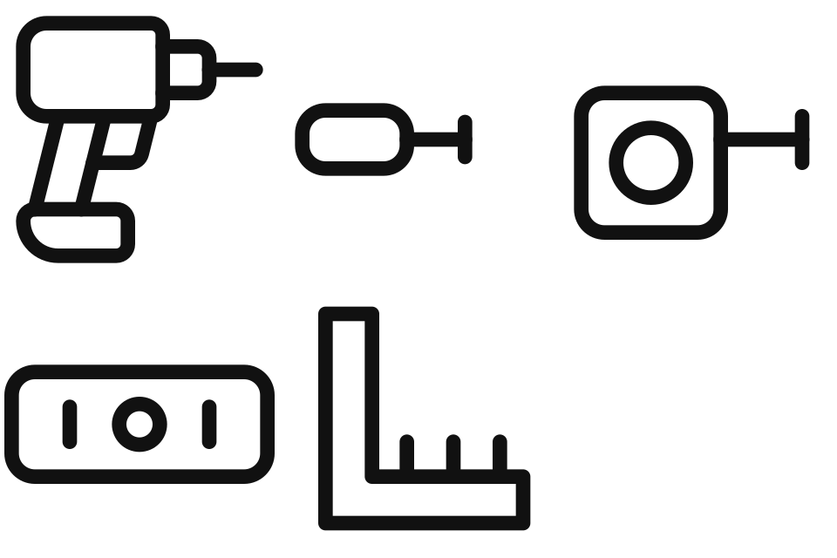
prosjekter/hanna/docs/img/ikon/verktoy.png
